alex-a11ahar/SolarEye-Security-System/Status Update 3 template.pptx.pdf

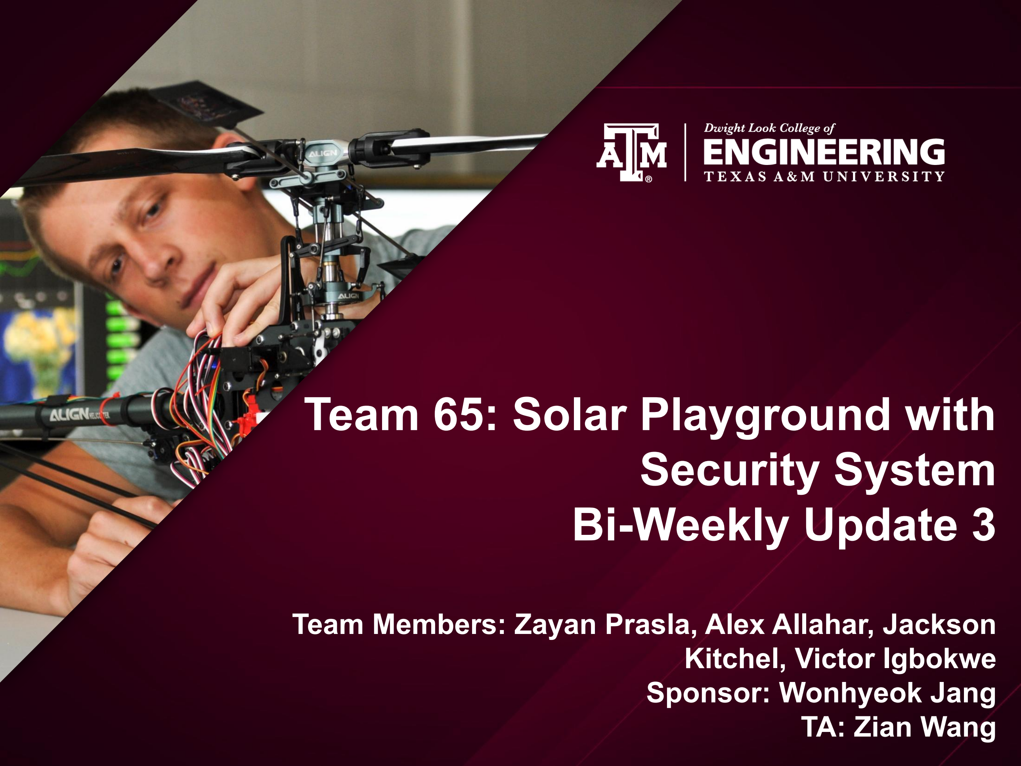
[picture p125: page 1]

# Team 65: Solar Playground with Security System Bi-Weekly Update 3

Team Members: Zayan Prasla, Alex Allahar, Jackson Kitchel, Victor Igbokwe
Sponsor: Wonhyeok Jang
TA: Zian Wang

# Project Summary

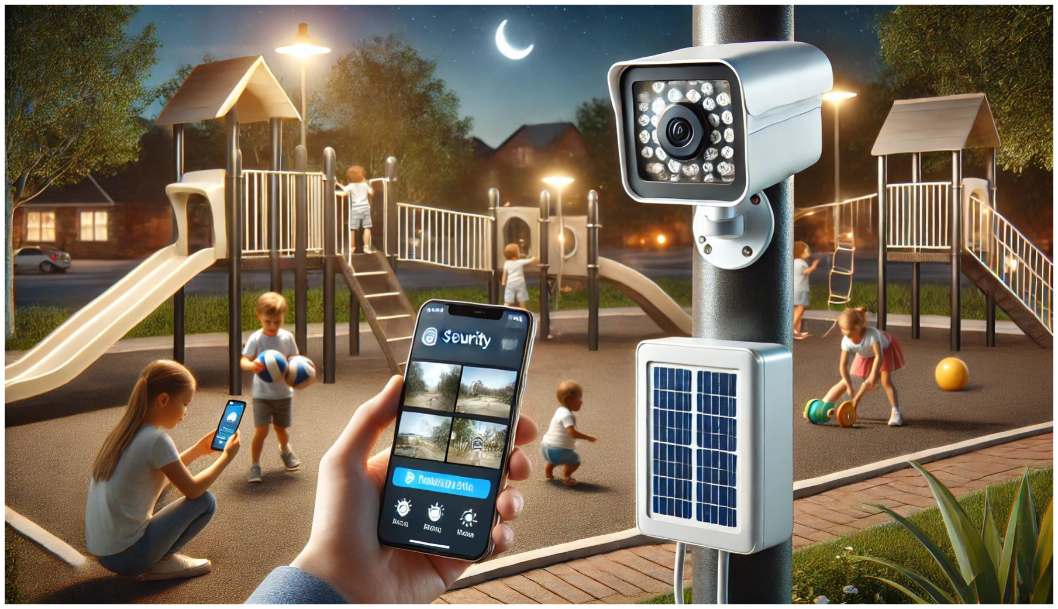
[picture p126: figure]

The SolarEye Security System is a solar-powered, autonomous
surveillance solution for playgrounds and parks.

It enhances security with
motion-activated cameras, real-time mobile alerts, LED deterrent lighting, and visitor charging stations.

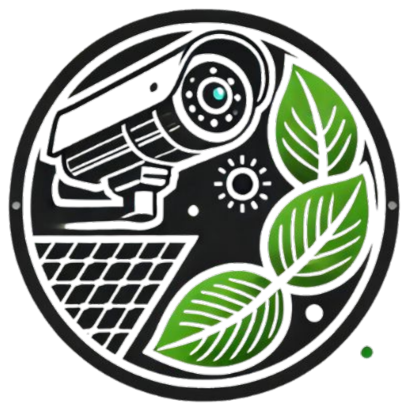
[picture p127: figure]

This eco-friendly system ensures continuous, cost-effective protection for private parks and properties.

# Project/Subsystem Overview

Red - Jackson Kitchel (Power Generation) Yellow - Victor Igbokwe (Power Distribution) Green - Alex Allahar (Microprocessor & Sensors) Blue - Zayan Prasla (Network & Application)

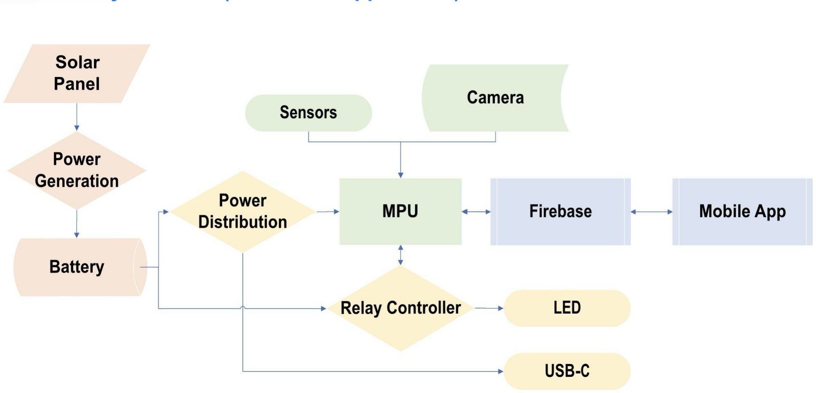
[picture p128: figure]

# Project Timeline

New PCBs
Ordered/
Received
(completed
02/03)

Integration
of MPU and
Application
subsystems
(to
completed
02/25)

Integration
of Power
Delivery
system with
MPU (to
complete by
02/25)

Integration of
Power
Generation
System with
Power
Delivery
System
(to complete
by 02/28)

Final
Integration
(to complete
by 03/03)

System Test
(to complete
by 03/10)

Validation
(to
complete by
03/20)

Demo and
Report
(to
complete
by 04/25)

# Power Generation

Accomplishments since last update 12 hrs of effort

Ongoing progress/problems and plans until the next presentation
- Both boards soldered
experienced issue of a
capacitor burning up
- Issue was found to be
component rated for wrong
amperage
- New component arrives
tomorrow
- Integrate with power distribution subsystem
- Test Current and Voltage sensor outputs with MCU
subsystem

# Power Generation

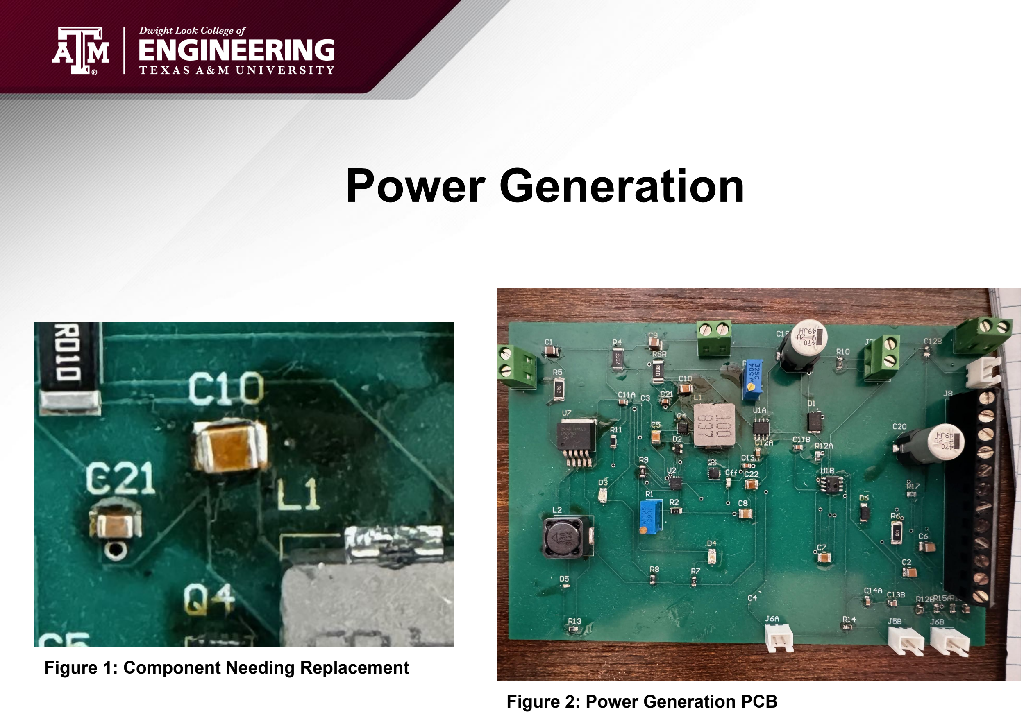
[picture p129: page 6]

Figure 1: Component Needing Replacement

Figure 2: Power Generation PCB

# Power Distribution

Accomplishments since last update 16 hrs of effort | Ongoing progress/problems and plans until the next presentation
❖ Successful Integration with Raspberry Pi MPU ❖ Soldered Relay Control module PCB | ❖ Validate Buck converter Integration for all modes of operation on MPU. ❖ Integration of relay control module PCB with Microprocessor system. ❖ Integration with

# Power Distribution

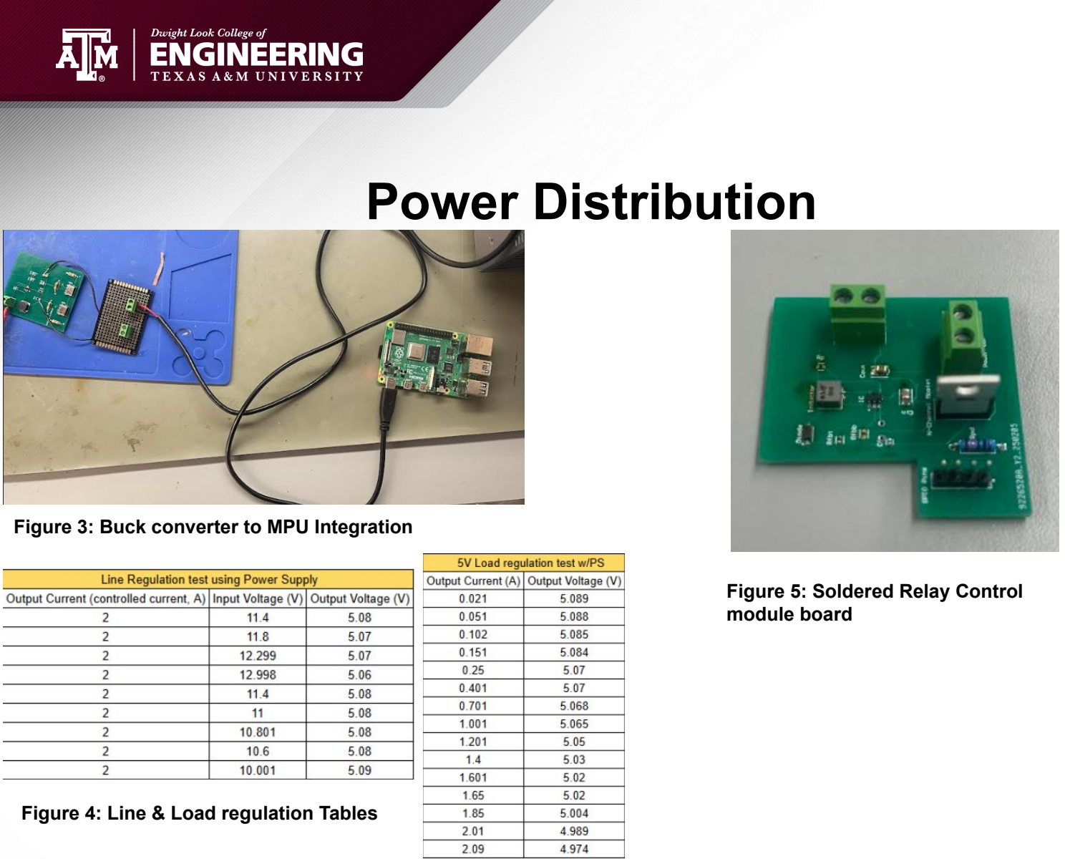
[picture p130: page 8]

Figure 3: Buck converter to MPU Integration

Figure 5: Soldered Relay Control module board

Figure 4: Line & Load regulation Tables

# Microprocessor & Sensors

Alex Allahar

Accomplishments since last update 17 hrs of effort

Ongoing progress/problems and plans until the next presentation ❖ Completed Integration of MPU with SolarEye App
❖ Integrated MPU with Buck Converter PCB
❖ Validated event detection to app delay

❖ Validate All Modes of Operation on Buck Converter PCB
❖ Validate Video Footage on Mobile App
❖ Complete Integration of Relay Controller PCB with MPU.
❖ Functionality Testing of App controlling Camera, LED, and sensor

# Microprocessor & Sensors

Alex Allahar

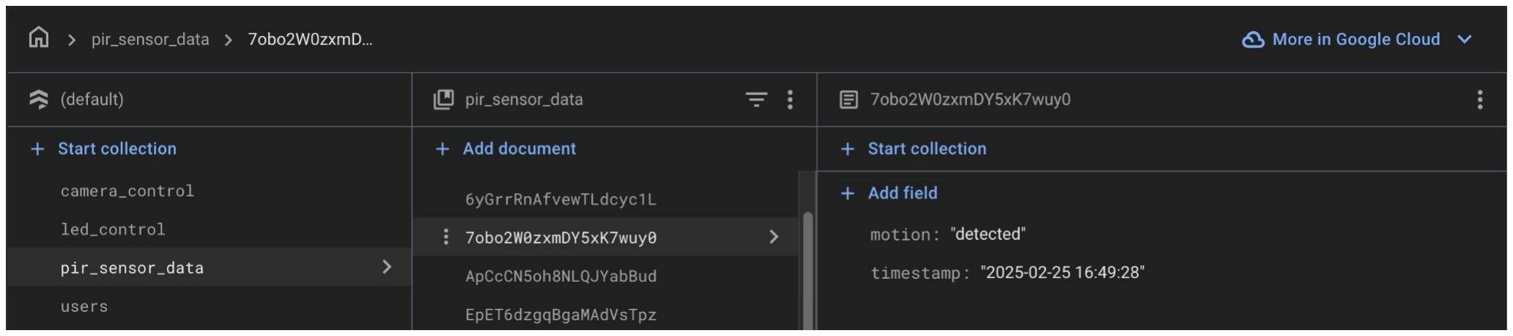
[picture p131: figure]

Figure 8: Event Detection Testcase Terminal

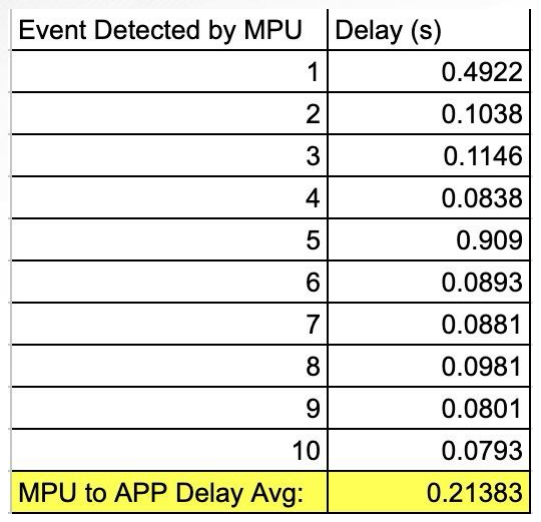
[picture p132: figure]

Figure 7: Firestore App Event History Database

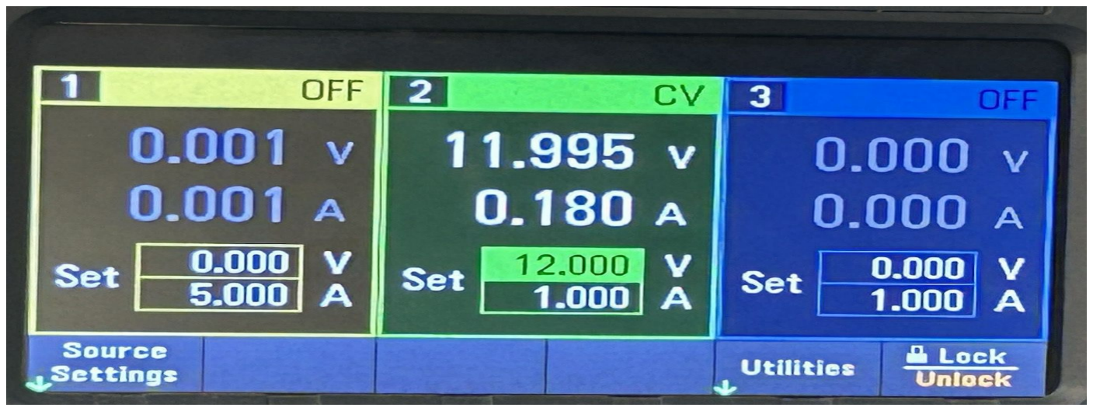
[picture p133: figure]

Figure 9: MPU Peak Current on Buck Converter PCB

Figure 6: MPU to App Delay Table

# Application & Network

Accomplishments since last update 12 hrs of effort

Ongoing progress/problems and plans until the next presentation ❖ Completed Integration between App and MPU
❖ Complete Camera/LED controls from app to Firebase to MPU ❖ Completed testing all backend security
❖ Instant updates to Event History

❖ Video and picture transfer from MPU to App
❖ Power level data
communication (Battery Level Graph)
❖ Lower power mode
❖ Live Streaming
❖ Ongoing updates to the
Frontend

# Application & Network

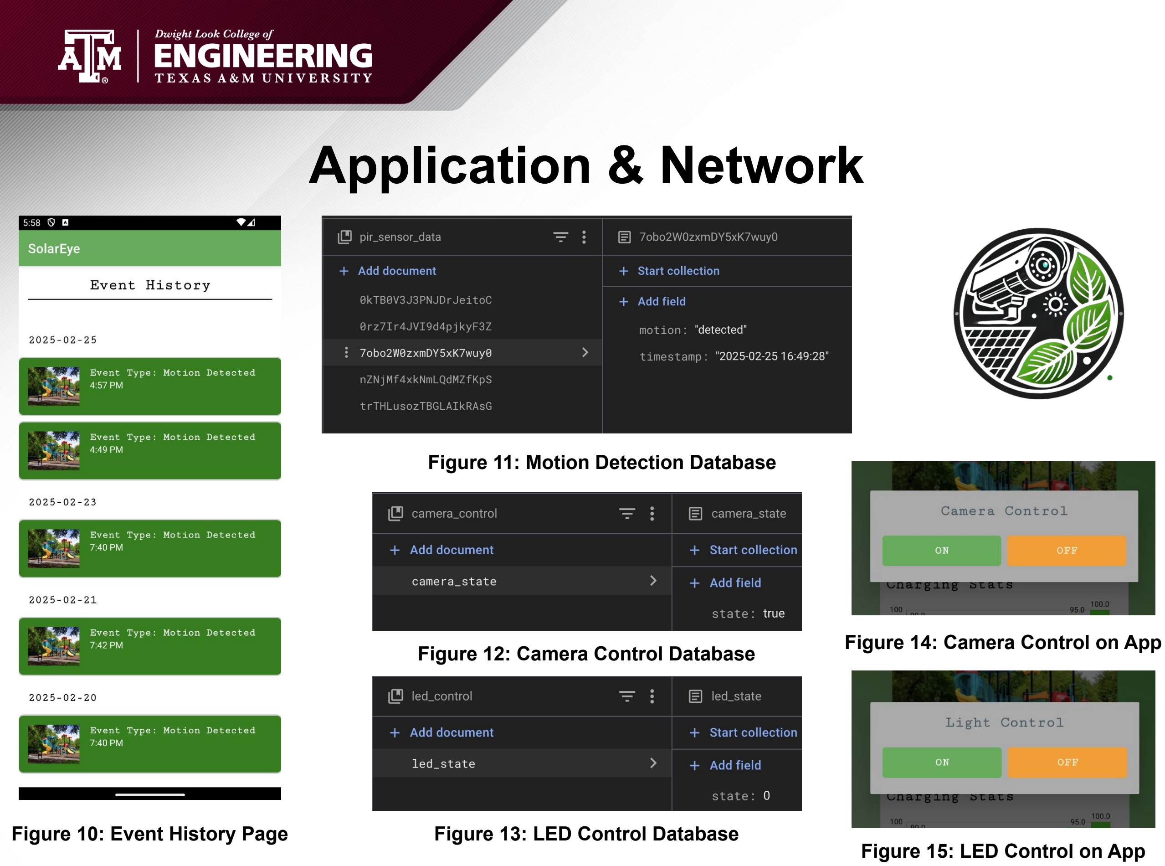
[picture p134: page 12]

Figure 10: Event History Page

Figure 11: Motion Detection Database

Figure 12: Camera Control Database

Figure 13: LED Control Database

Figure 14: Camera Control on App

Figure 15: LED Control on App

## Execution & Validation Plan

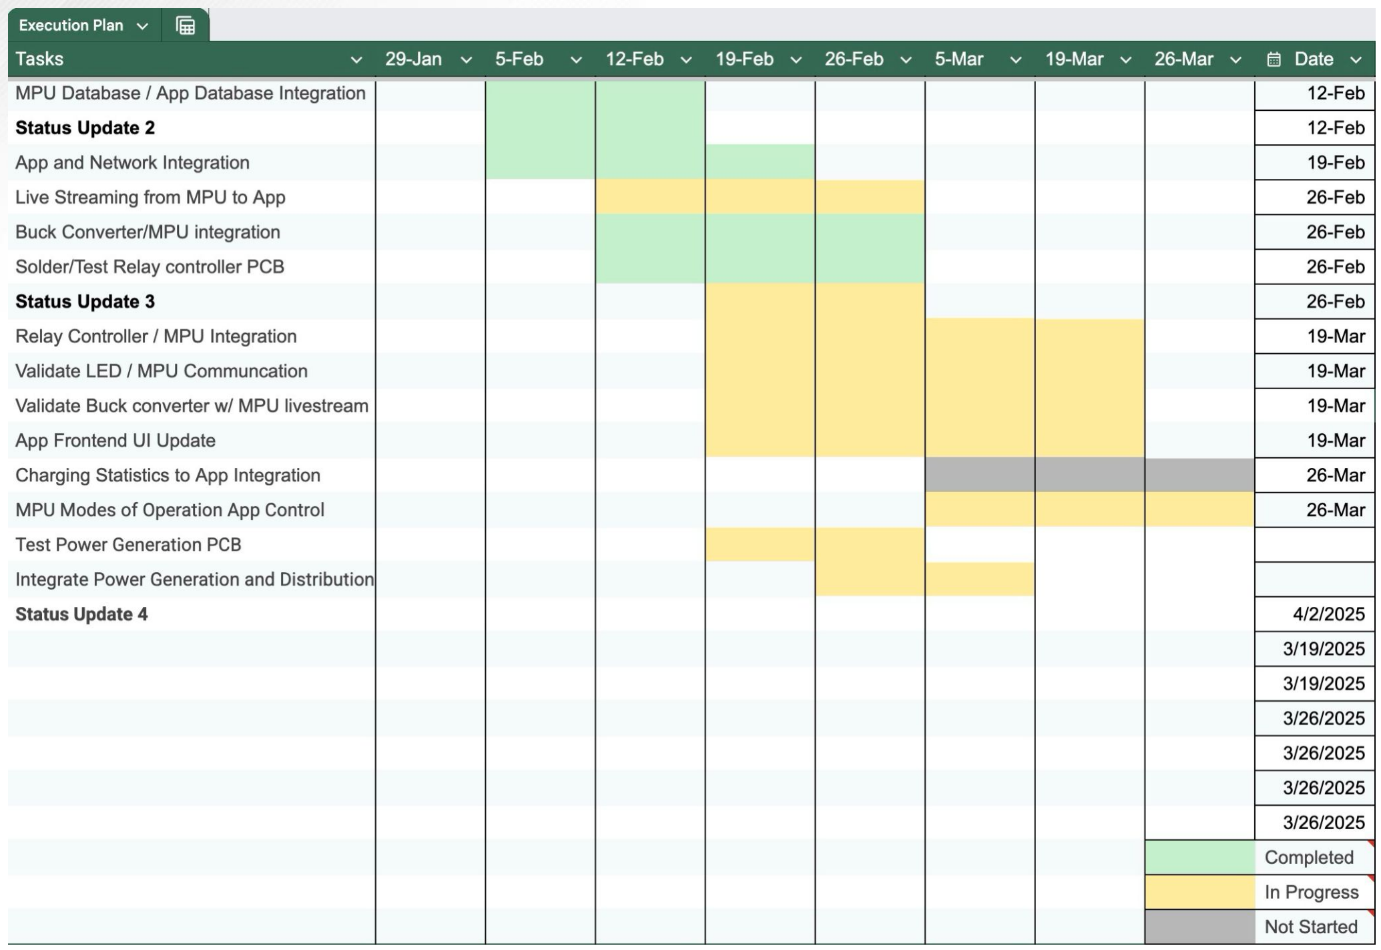
[picture p135: figure]

## Execution & Validation Plan

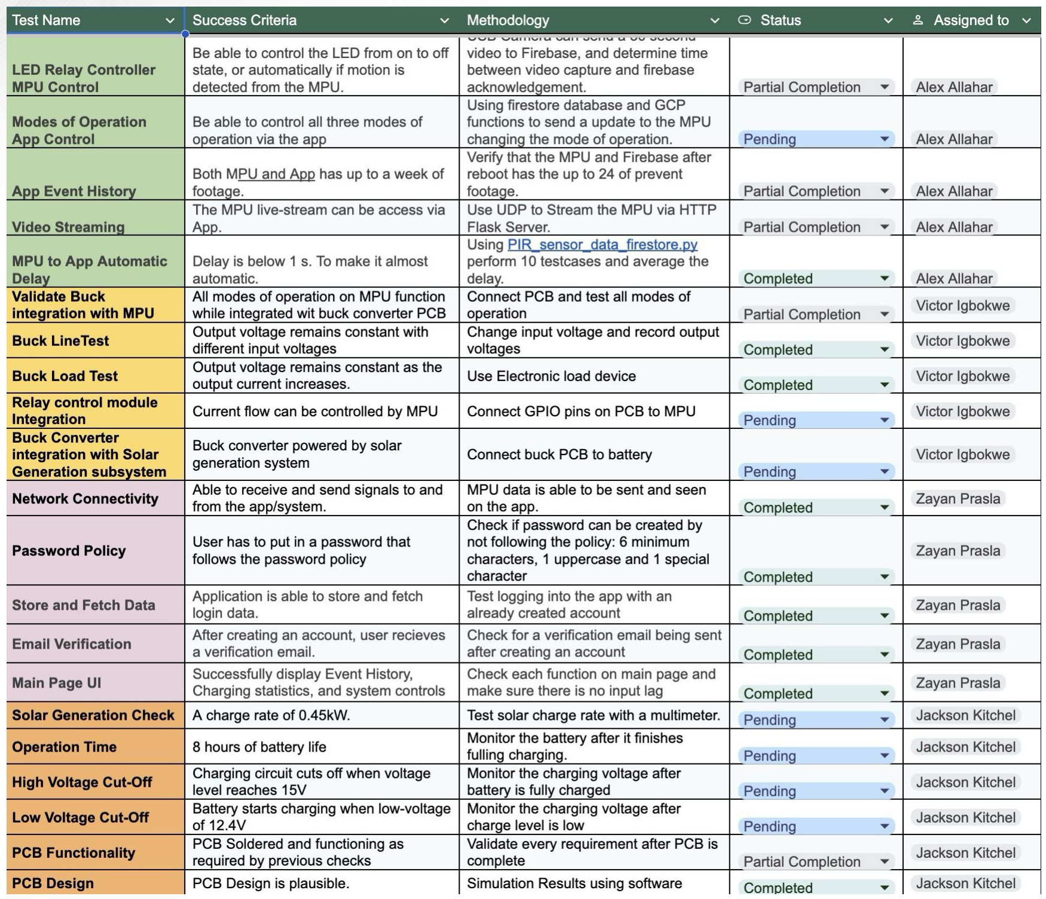
[picture p136: figure]

# Thank You
