alex-a11ahar/SolarEye-Security-System/Status Update 4 template.pptx.pdf

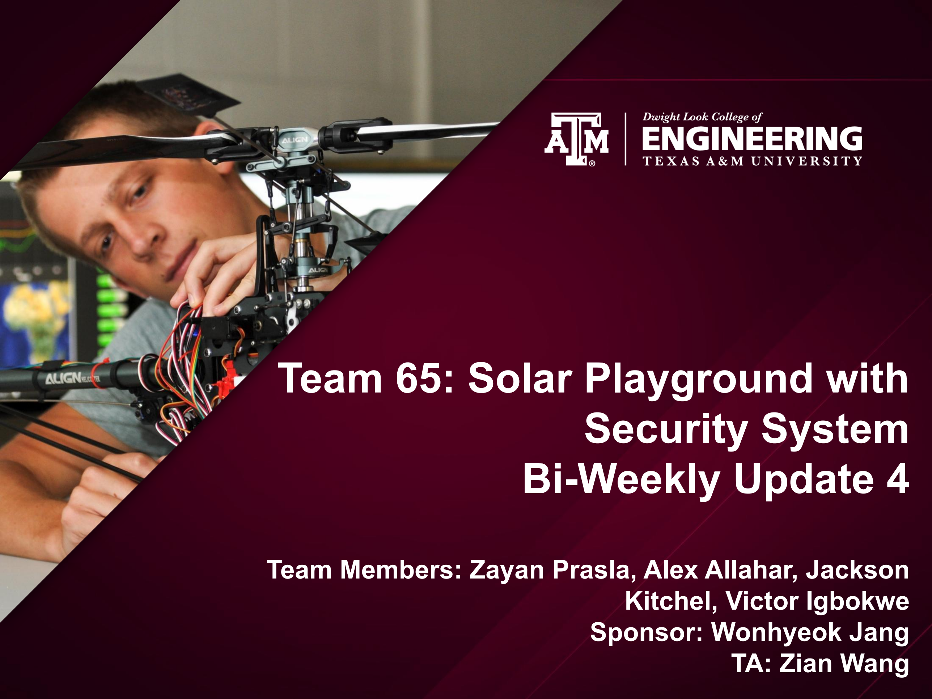
[picture p137: page 1]

# Team 65: Solar Playground with Security System Bi-Weekly Update 4

Team Members: Zayan Prasla, Alex Allahar, Jackson Kitchel, Victor Igbokwe
Sponsor: Wonhyeok Jang
TA: Zian Wang

# Project Summary


The SolarEye Security System is a solar-powered, autonomous
surveillance solution for playgrounds and parks.

It enhances security with
motion-activated cameras, real-time mobile alerts, LED deterrent lighting, and visitor charging stations.


This eco-friendly system ensures continuous, cost-effective protection for private parks and properties.

## Integrated System Diagram (Hardware)

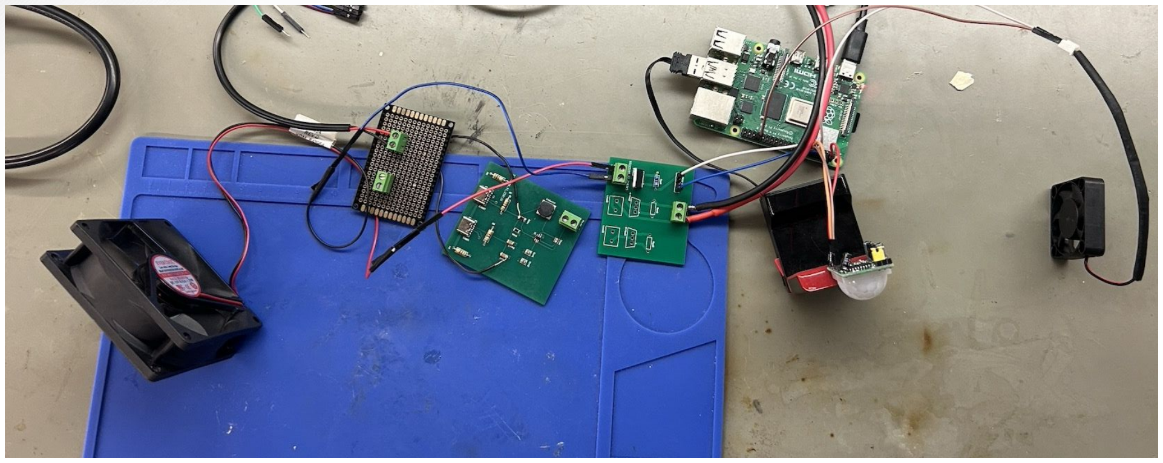
[picture p138: figure]

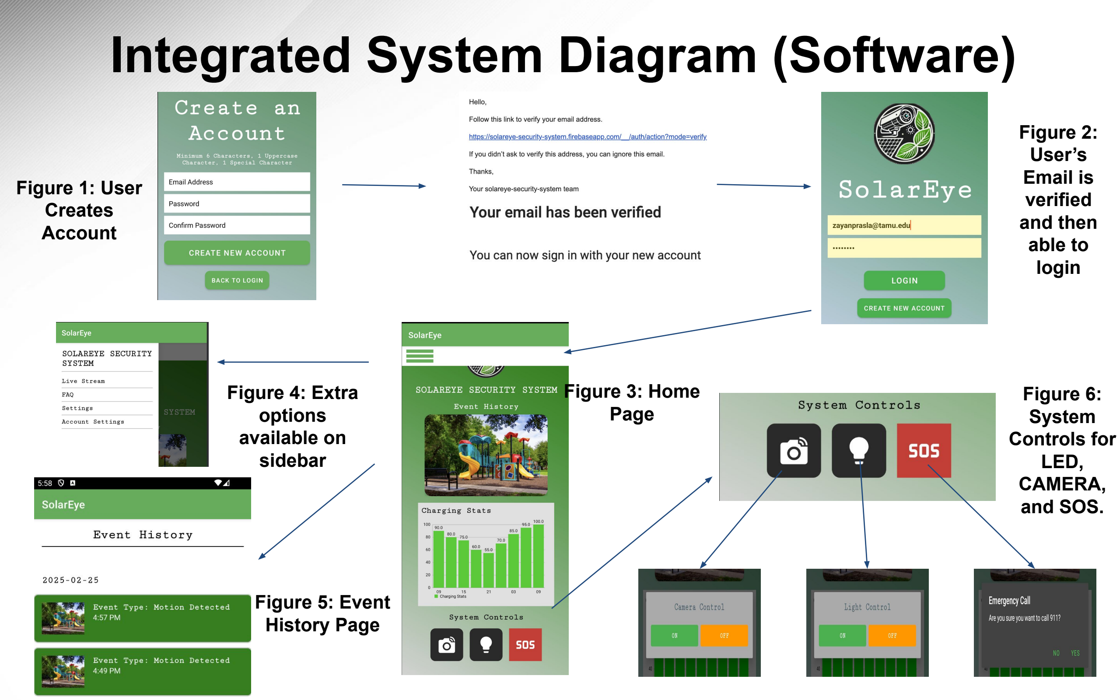
[picture p139: figure]
Integrated System Diagram (Software); Figure 1: User Creates Account; Figure 2: User’s Email is verified and then able to login; Figure 3: Home Page; Figure 6: System Controls for LED, CAMERA, and SOS.; Figure 5: Event History Page; Figure 4: Extra options available on sidebar

# Project Timeline

New PCBs
Ordered/
Received
(completed
02/03)

Integration
of MPU and
Application
subsystems
(to
completed
02/25)

Integration
of Power
Delivery
system with
MPU (to
complete by
02/25)

Integration of
Power
Generation
System with
Power
Delivery
System
(to complete
by 03/26)

System
Housing
(to complete
by 03/28)

Final
Integration
(to complete
by 04/10)

Validation
(to
complete by
04/20)

Demo and
Report
(to
complete
by 04/25)

# Jackson Kitchel

Accomplishments since last update 30 hrs of effort | Ongoing progress/problems and plans until the next presentation
❖ PCB was redesigned to fix capacitor problem and consolidate ❖ New PCB was soldered and tested ❖ Integration with solar panel and battery complete and tested | ❖ Integrate sensor outputs with MCU subsystem ❖ Start Housing ❖ Finish testing integration with power delivery subsystem

# Jackson Kitchel

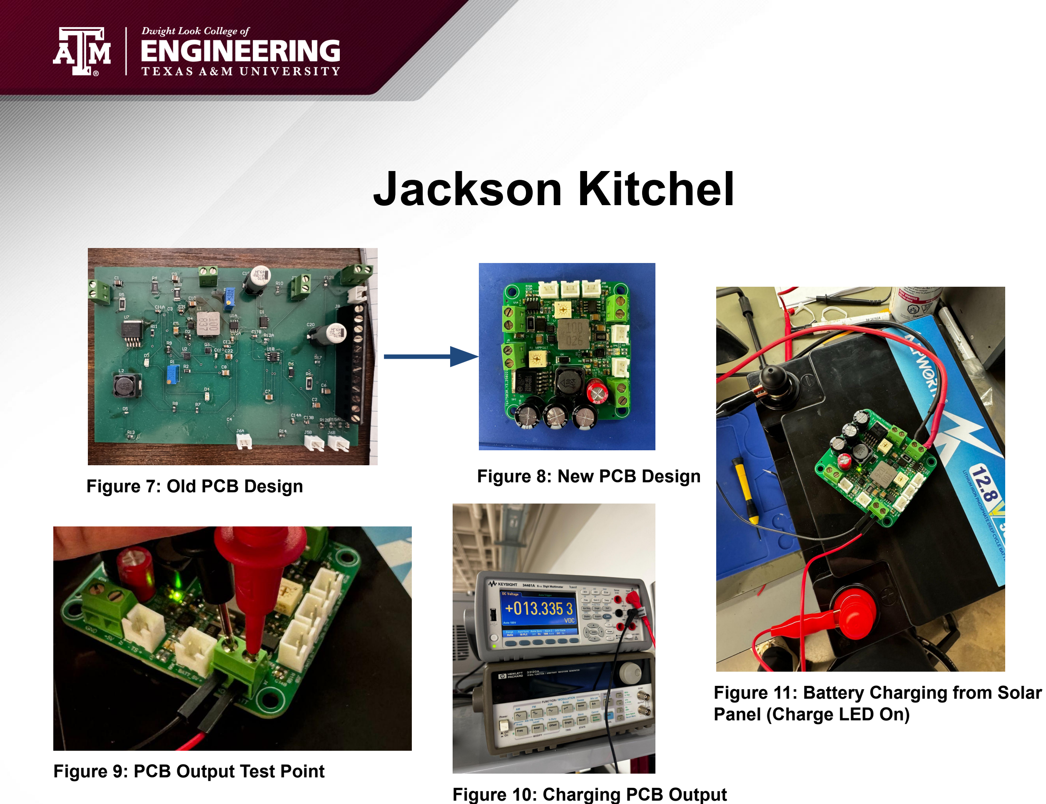
[picture p140: page 7]

Figure 7: Old PCB Design | Figure 8: New PCB Design

Figure 11: Battery Charging from Solar Panel (Charge LED On)

Figure 10: Charging PCB Output

Figure 9: PCB Output Test Point

# Victor Igbokwe

Accomplishments since last update 12 hrs of effort | Ongoing progress/problems and plans until the next presentation
❖ Integration of Power Distribution and MPU system completed ❖ Validated power outputs for different modes of operation with MPU | ❖ Integration with Power Generation system. ❖ Design/Build Housing for Circuit boards(During capstone blitz).

# Victor Igbokwe

Mode of Operation | Power Consumption(A)
Idle | 1.88 A
Event Detection | 3.65 A
Live Streaming | 2.15A

Figure 12: MPU Operating Modes and Corresponding Power Consumption Table

Media 1: Video showing the Buck converter supplying
power to MPU while
livestreaming

# Alex Allahar

Accomplishments since last update 8 hrs of effort | Ongoing progress/problems and plans until the next presentation
❖ Integrated Relay Controller PCB with MPU. ❖ Validate Event History on App Database ❖ Verified MPU / APP controls LED and cooling fans. | ❖ Validate Event History on Mobile App ❖ Start housing during Blitz.

# Alex Allahar

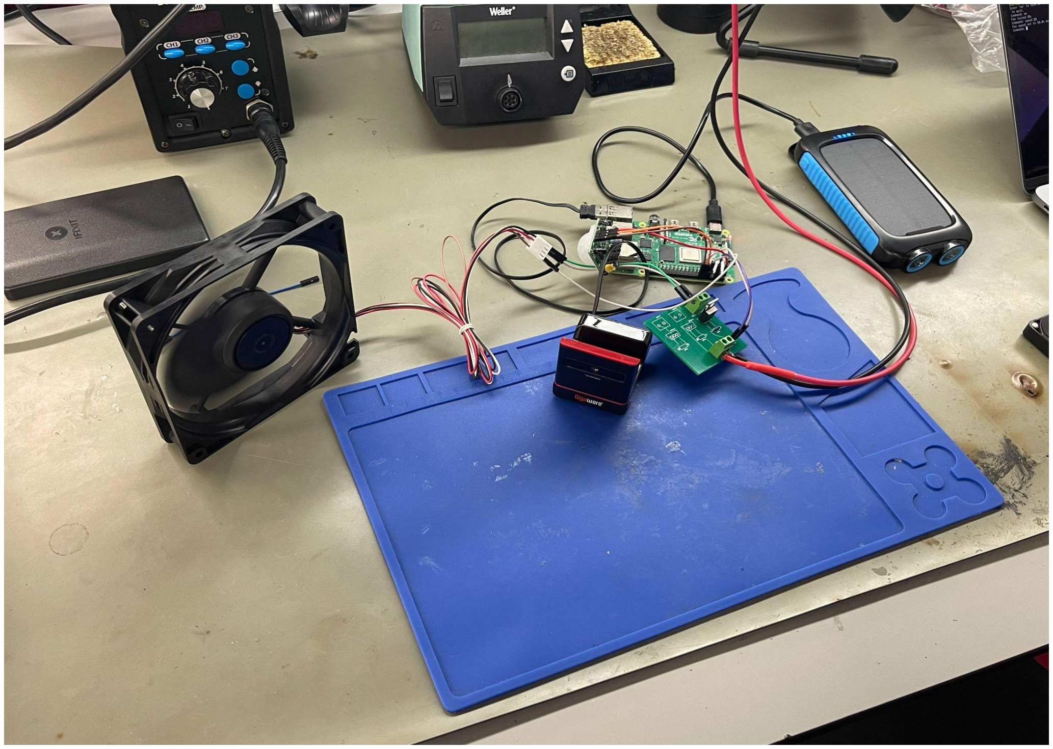
[picture p141: figure]

Figure 13: Fan Component Testing Setup and Table

Component | Power Consumption(A)
Small Fan (Fixed) | 0.6 A
Medium Fan (Fixed) | 1.16 A
Large Fan (Variable) | 7.017 A (100 %)

# Alex Allahar

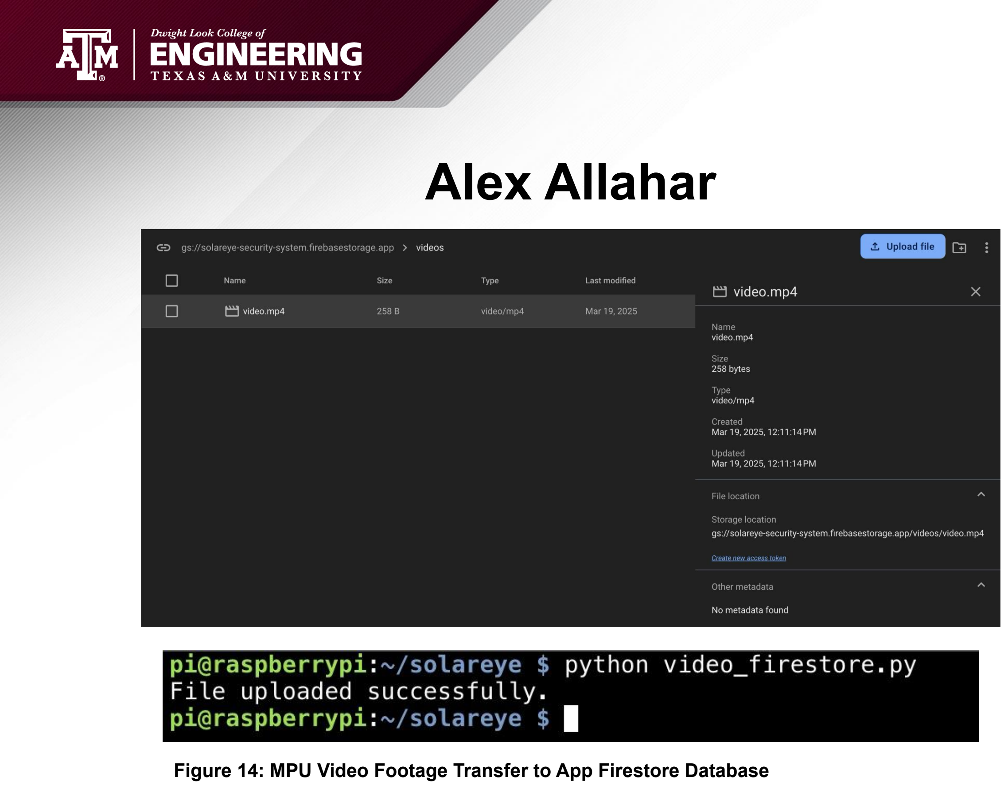
[picture p142: page 12]

Figure 14: MPU Video Footage Transfer to App Firestore Database

# Zayan Prasla

Accomplishments since last update 7 hrs of effort | Ongoing progress/problems and plans until the next presentation
❖ Validated all button communication from App to MCU ❖ Continuous tweaks to the frontend to for smoothest app experience | ❖ Validate thumbnail (picture)/video transfer from mcu to app ❖ Validate live streaming ❖ Power level communication ❖ Validate Low power mode

# Zayan Prasla

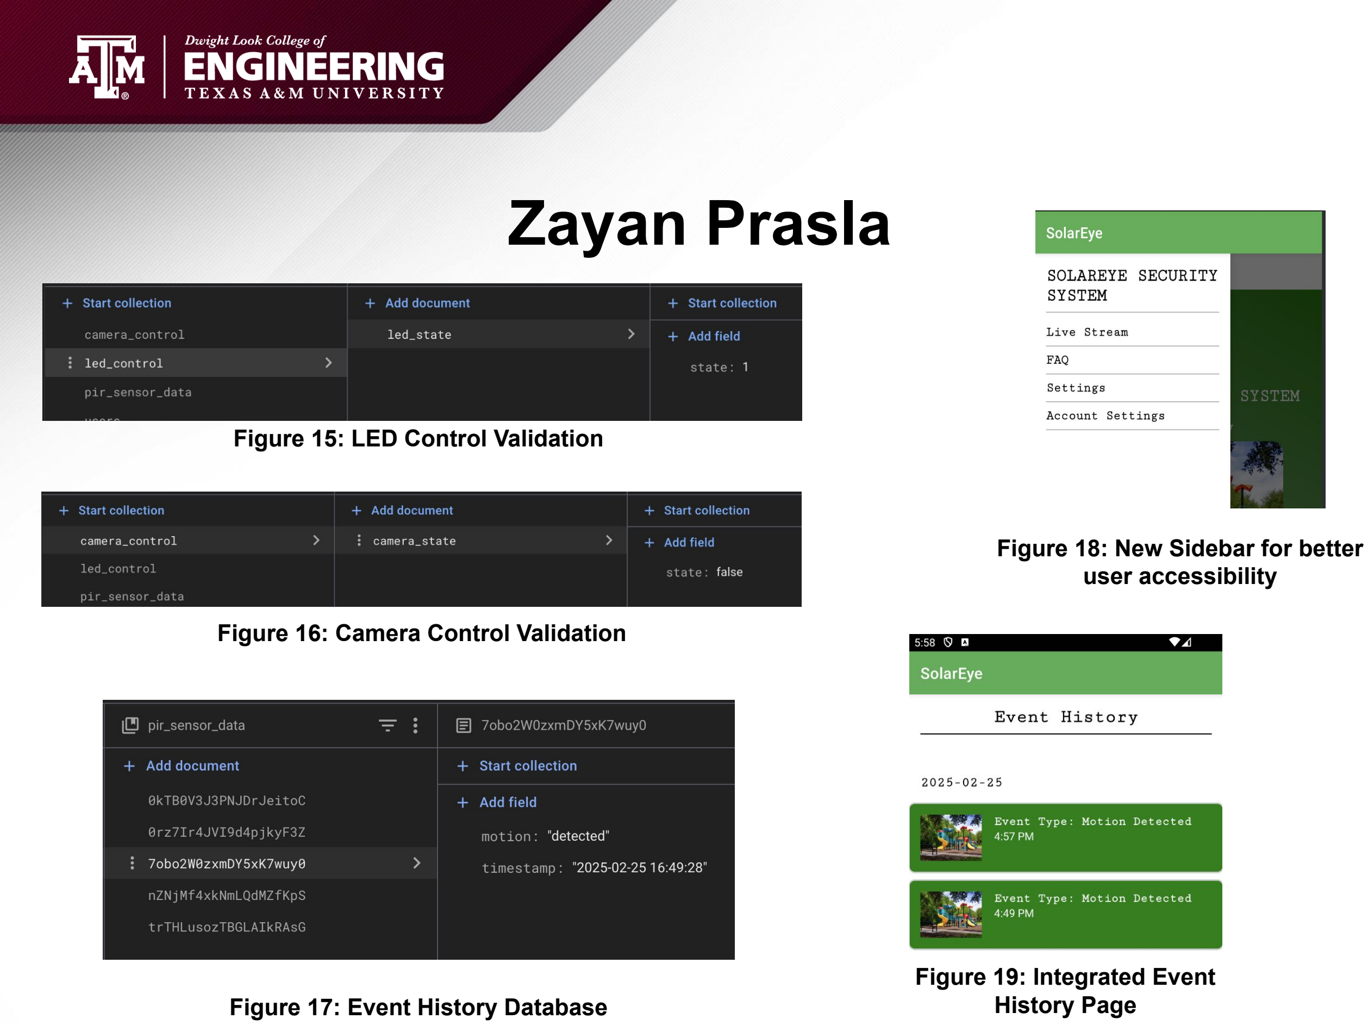
[picture p143: page 14]

Figure 18: New Sidebar for better user accessibility

Figure 15: LED Control Validation

Figure 16: Camera Control Validation

Figure 17: Event History Database

Figure 19: Integrated Event History Page

# Execution Plan

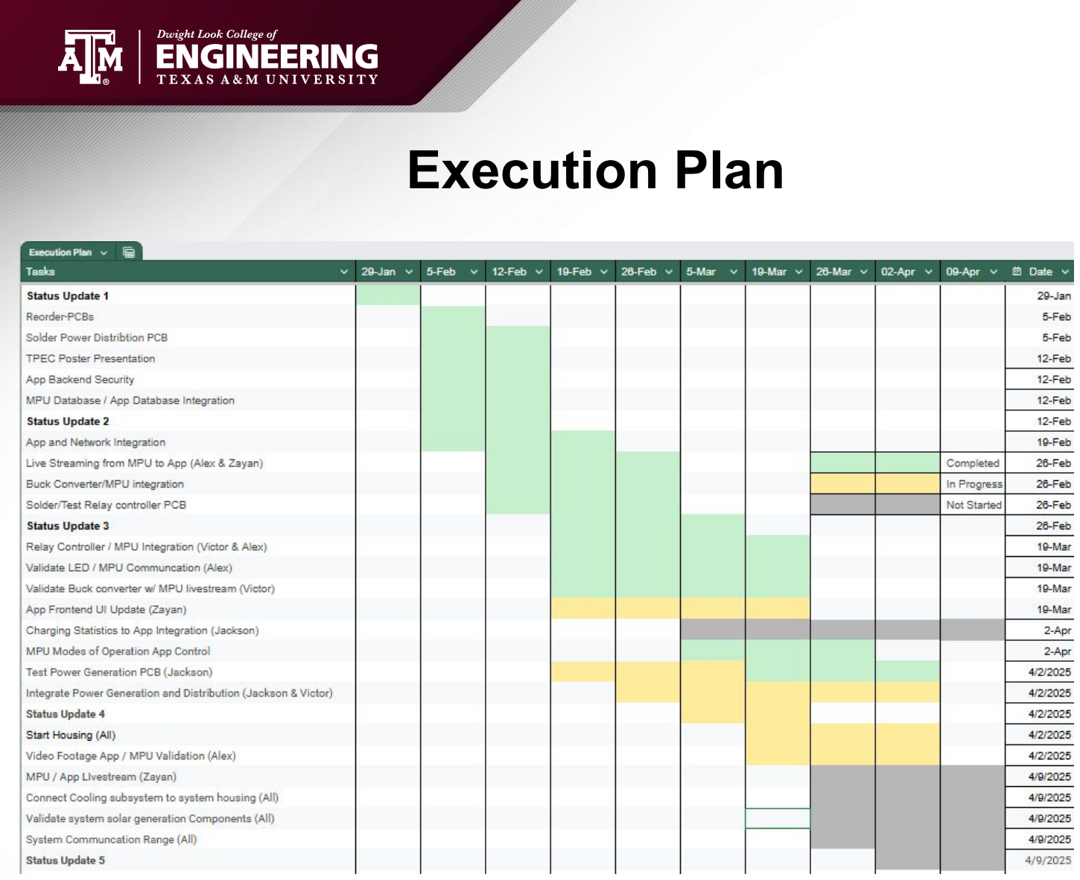
[picture p144: page 15]

# SYSTEM Validation Plan

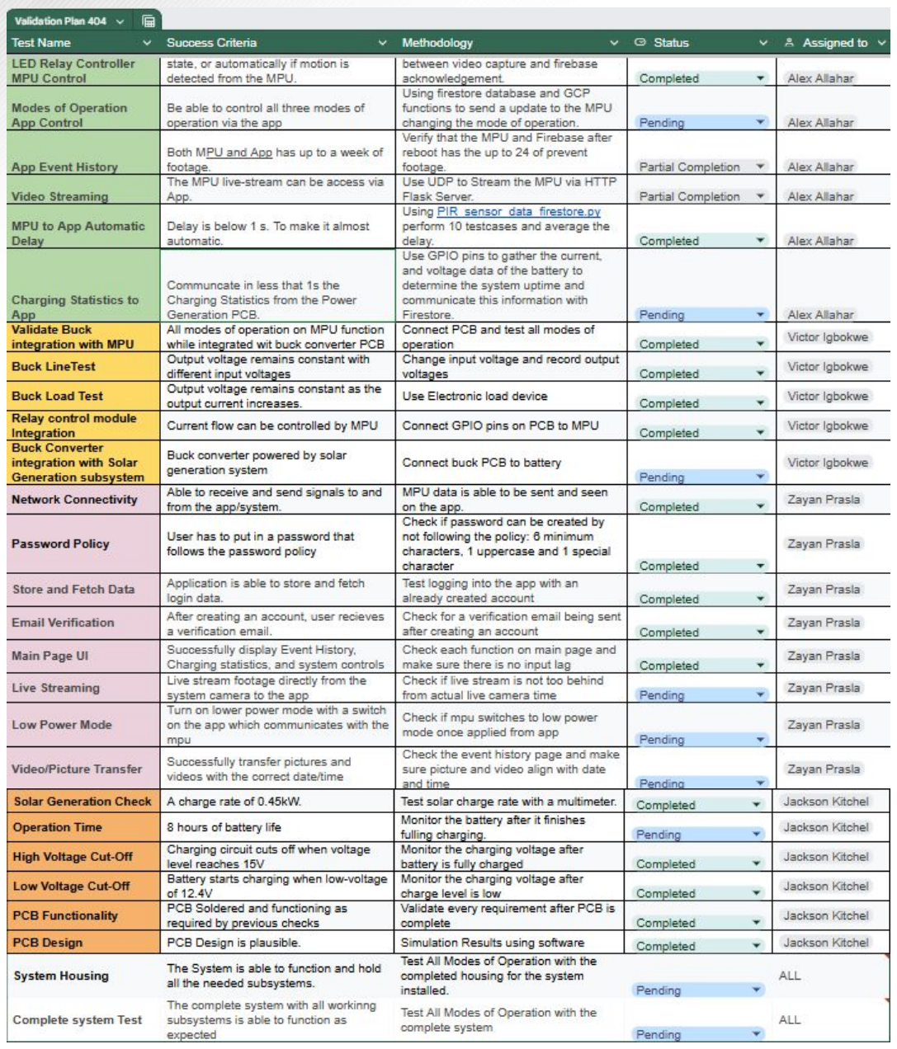
[picture p145: figure]

# Thank You!
