alex-a11ahar/SolarEye-Security-System/Status Update 5 template.pptx.pdf

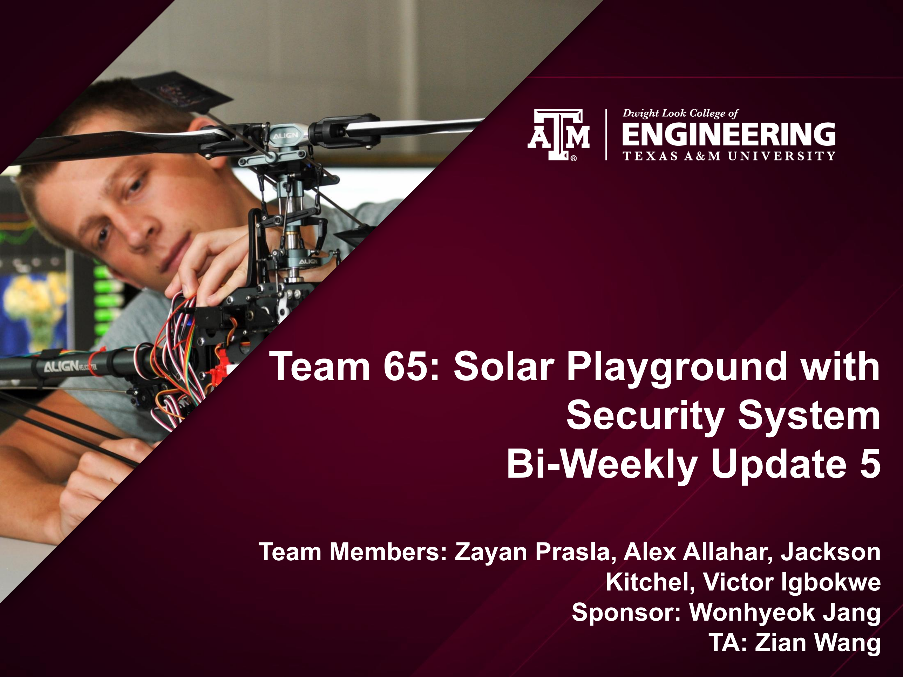
[picture p146: page 1]

# Team 65: Solar Playground with Security System Bi-Weekly Update 5

Team Members: Zayan Prasla, Alex Allahar, Jackson Kitchel, Victor Igbokwe
Sponsor: Wonhyeok Jang
TA: Zian Wang

# Project Summary


The SolarEye Security System is a solar-powered, autonomous
surveillance solution for playgrounds and parks.

It enhances security with
motion-activated cameras, real-time mobile alerts, LED deterrent lighting, and visitor charging stations.


This eco-friendly system ensures continuous, cost-effective protection for private parks and properties.

## Integrated System Diagram (Hardware)

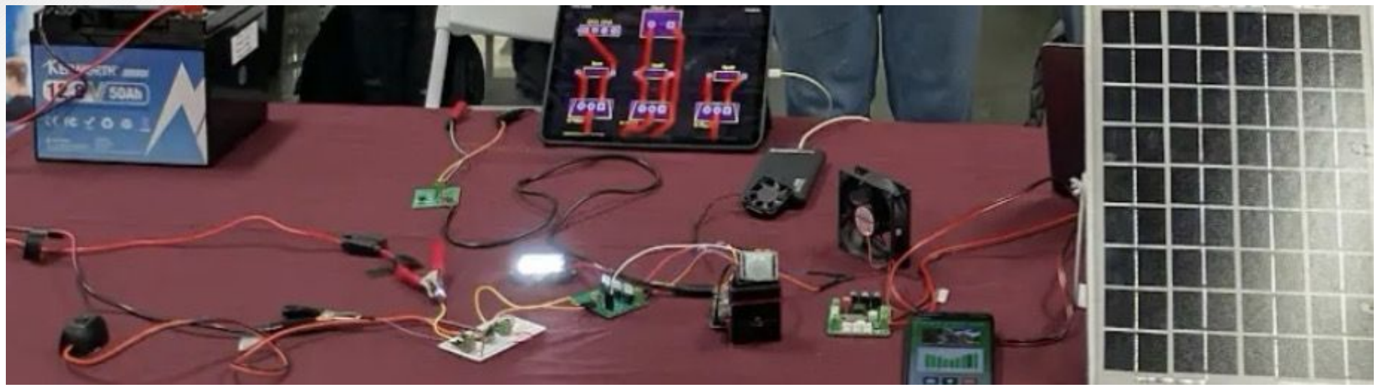
[picture p147: figure]

Figure 1: Full System Open Housing Diagram

# Integrated System Diagram (Software)

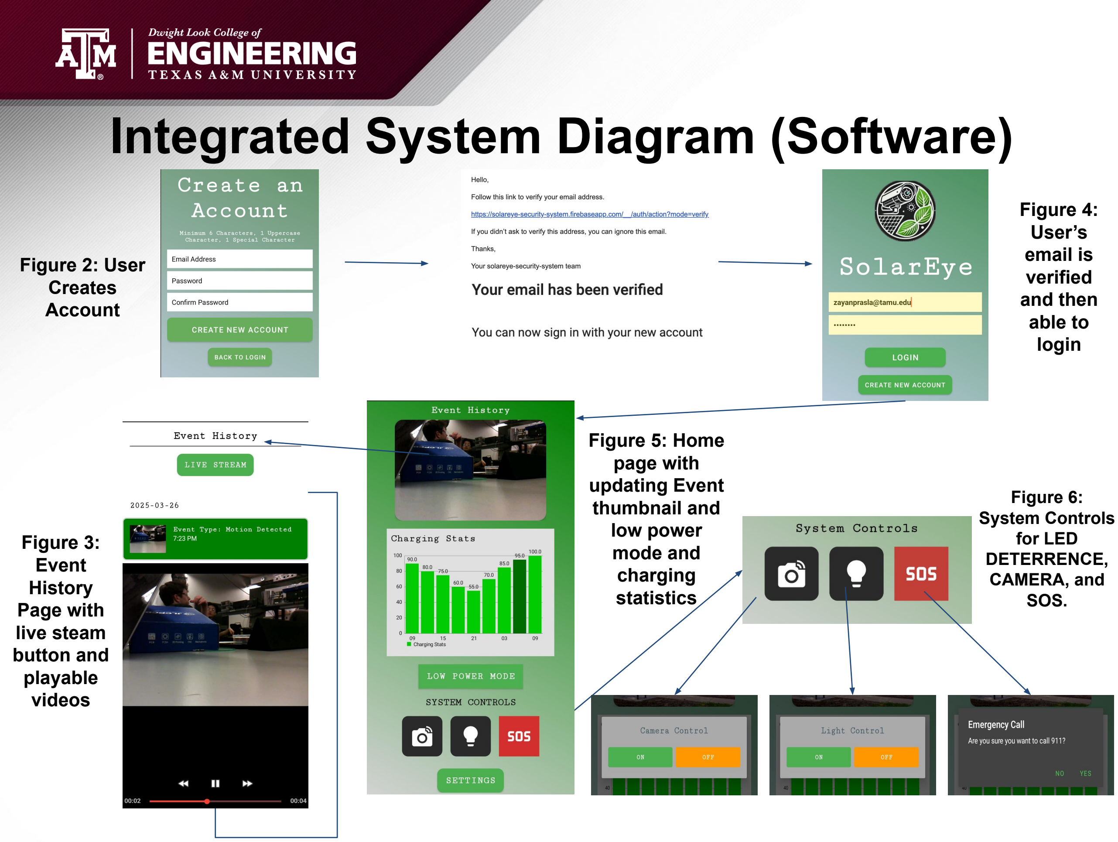
[picture p148: page 4]

Figure 2: User
Creates
Account

Figure 4:
User’s
email is
verified
and then
able to
login

Figure 5: Home
page with
updating Event
thumbnail and
low power
mode and
charging
statistics

Figure 6:
System Controls
for LED
DETERRENCE,
CAMERA, and
SOS.

Figure 3:
Event
History
Page with
live steam
button and
playable
videos

# Project Timeline

New PCBs
Ordered/
Received
(completed
02/03)

Integration
of MPU and
Application
subsystems
(to
completed
02/25)

Integration
of Power
Delivery
system with
MPU (to
complete by
02/25)

Integration of
Power
Generation
System with
Power
Delivery
System
(to complete
by 03/26)

Final
Integration
(to complete
by 04/10)

System
Housing
(to complete
by 04/10)

Validation
(to
complete by
04/20)

Demo and
Report
(to
complete
by 04/25)

# Jackson Kitchel

Accomplishments since last update 9 hrs of effort | Ongoing progress/problems and plans until the next presentation
❖ Sensors have been connected via ADC to MCU ❖ Finished integration with Power Distribution Subsystem | ❖ Finish setting up sensor algorithms in coordination with MCU subsystem ❖ Housing

# Jackson Kitchel

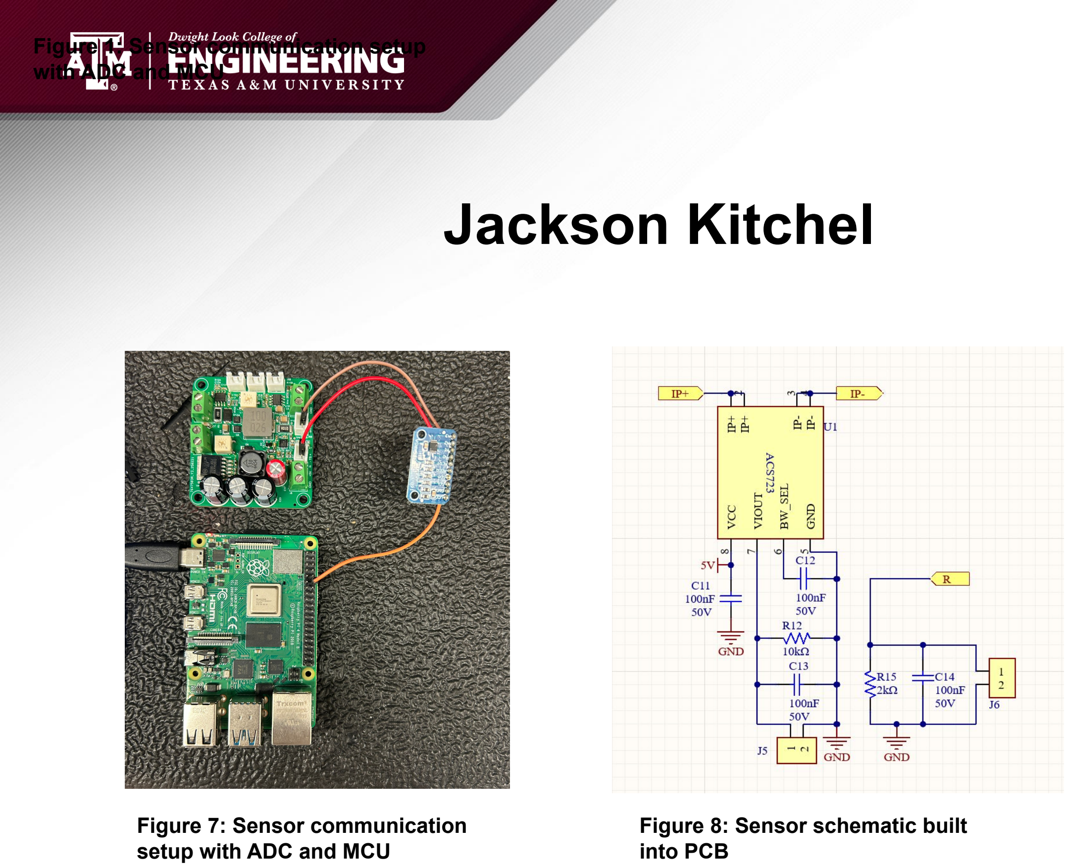
[picture p149: page 7]

Figure 7: Sensor communication setup with ADC and MCU

Figure 1: Sensor communication setup with ADC and MCU

Figure 8: Sensor schematic built into PCB

# Victor Igbokwe

Accomplishments since last update 13 hrs of effort | Ongoing progress/problems and plans until the next presentation
❖ Finished Integration with Power Generation Subsystem ❖ Created a Switchboard to improve safety when dealing with battery. | ❖ Finish Up Housing Box ❖ House PCBs and other devices in box

# Victor Igbokwe

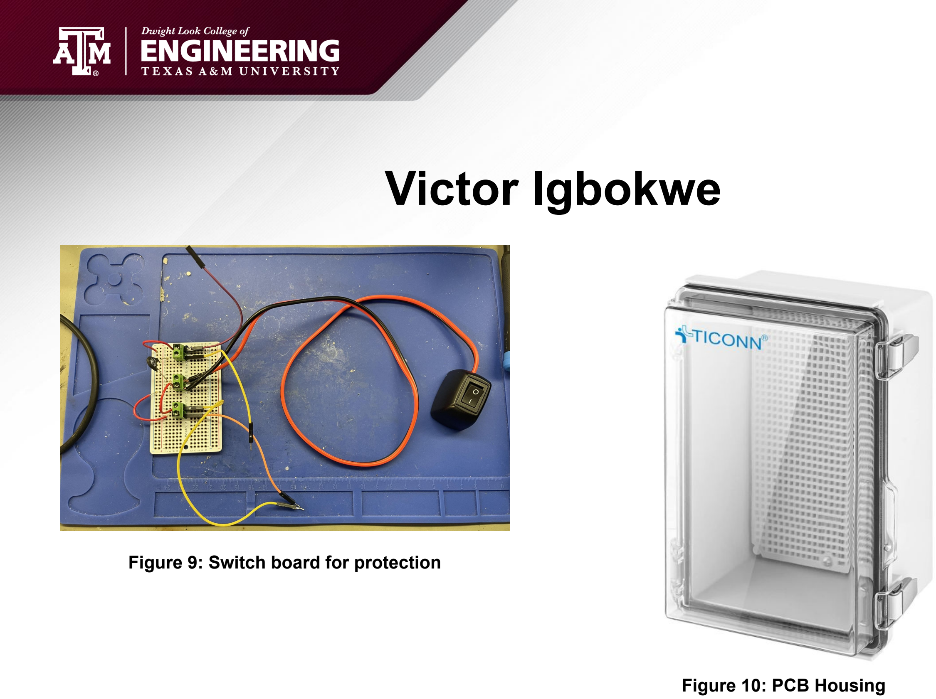
[picture p150: page 9]

Figure 9: Switch board for protection

Figure 10: PCB Housing

# Alex Allahar

Accomplishments since last update 12 hrs of effort | Ongoing progress/problems and plans until the next presentation
❖ Developed LED Deterrence Button for App ❖ Tested ADC I2C communication with Power Generation PCB | ❖ Replace Camera ❖ Validate Charging Statistics ❖ Complete Housing

# Alex Allahar

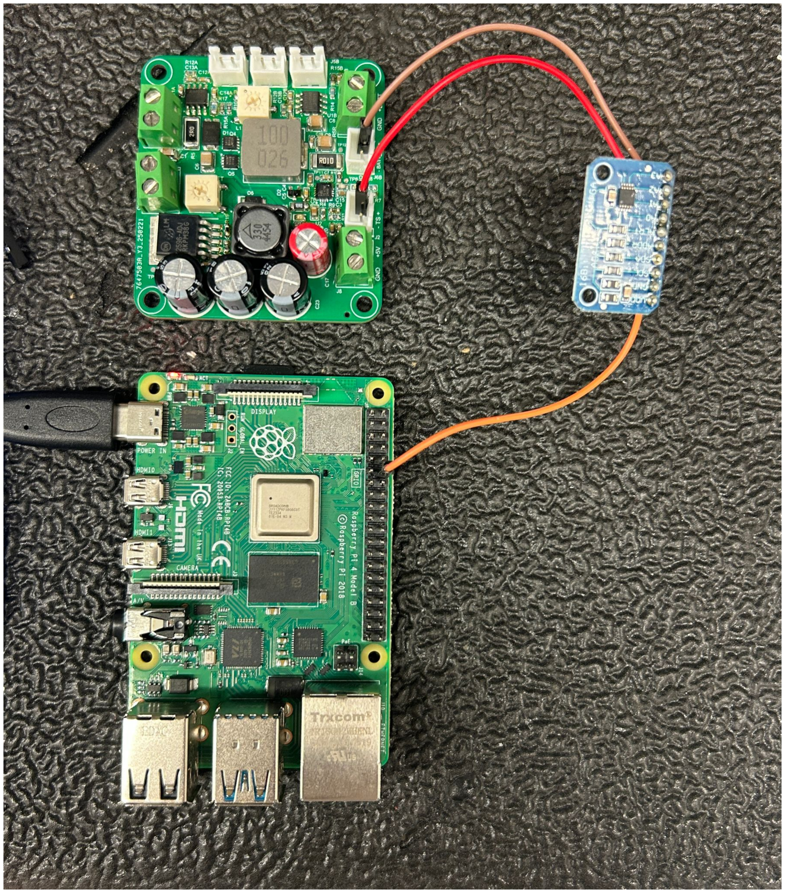
[picture p151: figure]
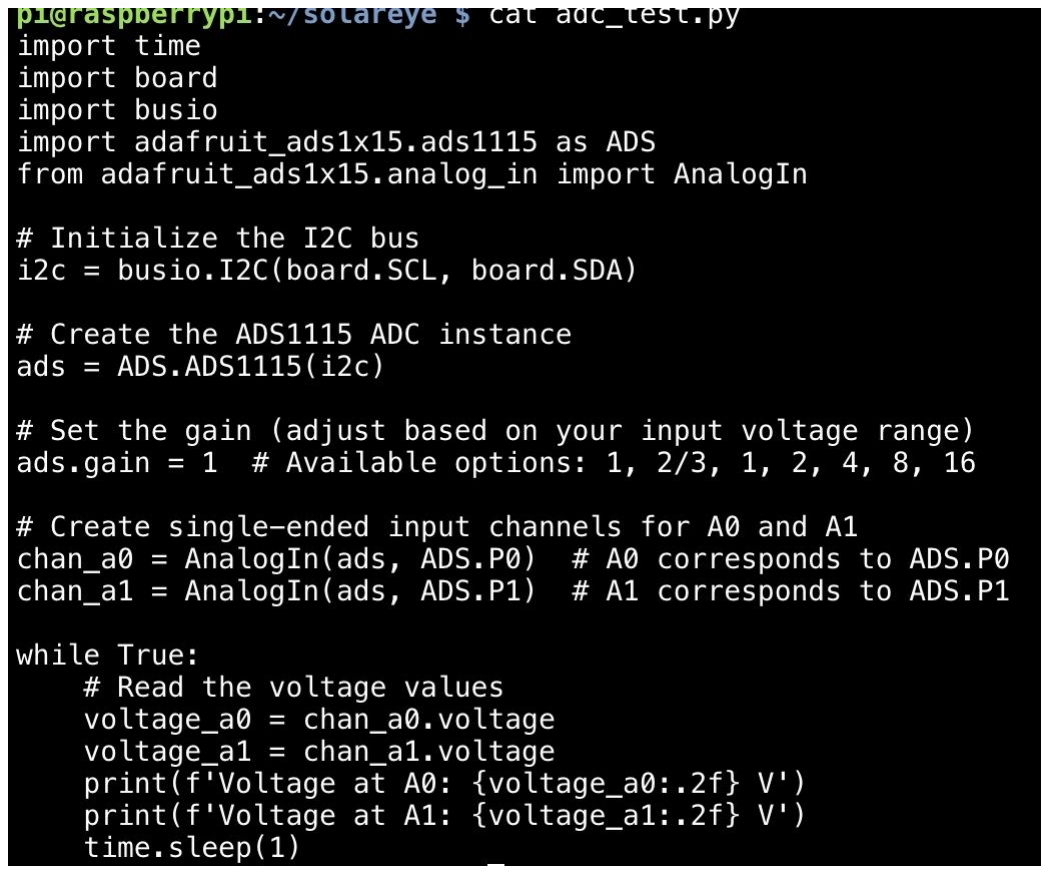
[picture p152: figure]

Figure 11: ADS 1115 Code / Setup

# Zayan Prasla

Accomplishments since last update 11 hrs of effort

Ongoing progress/problems and plans until the next presentation ❖ Successfully validated video data transfer from MCU to app ❖ Updated event history
thumbnail on home page to
dynamically display the latest detection
❖ Implemented buttons for live streaming and low power mode functionalities

❖ Validate/test Low Power mode ❖ Validate/test Live Streaming ❖ Validate/test charging statistics

# Zayan Prasla

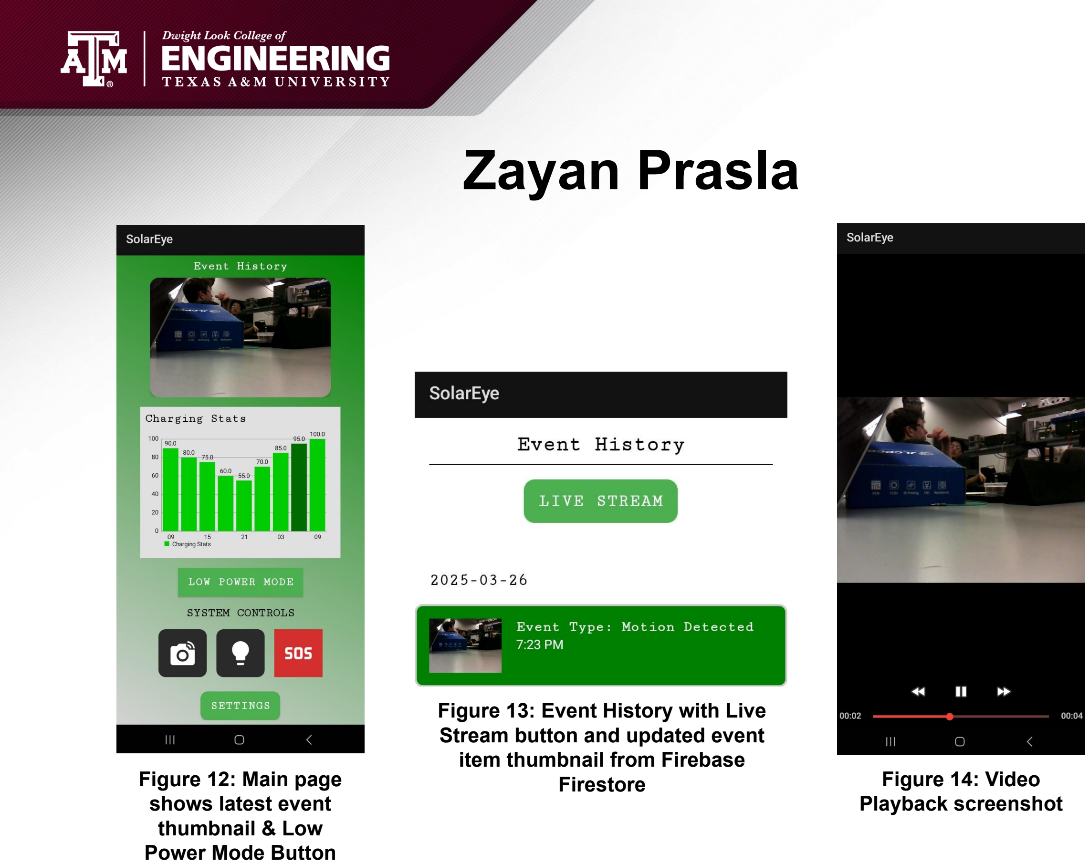
[picture p153: page 13]

Figure 12: Main page
shows latest event
thumbnail & Low
Power Mode Button

Figure 14: Video
Playback screenshot

Figure 13: Event History with Live Stream button and updated event item thumbnail from Firebase Firestore

# Execution Plan

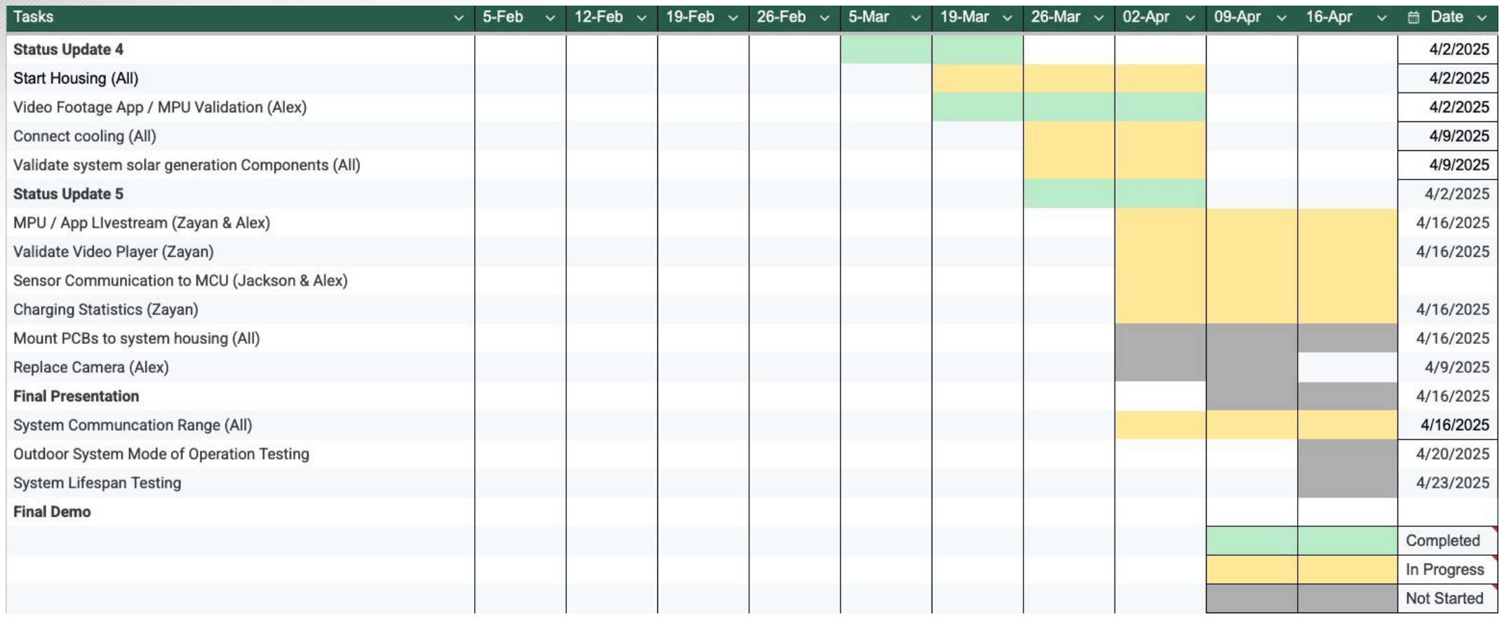
[picture p154: figure]

# SYSTEM Validation Plan Part 1

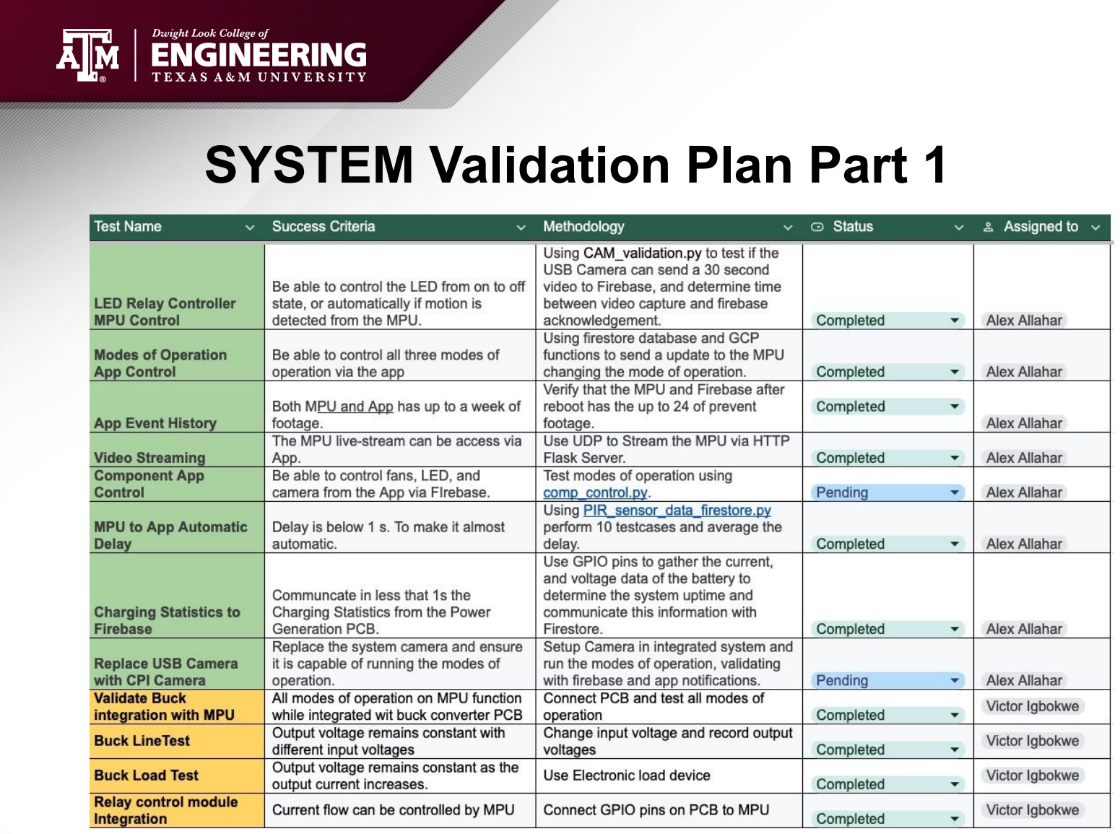
[picture p155: page 15]

# SYSTEM Validation Plan Part 2

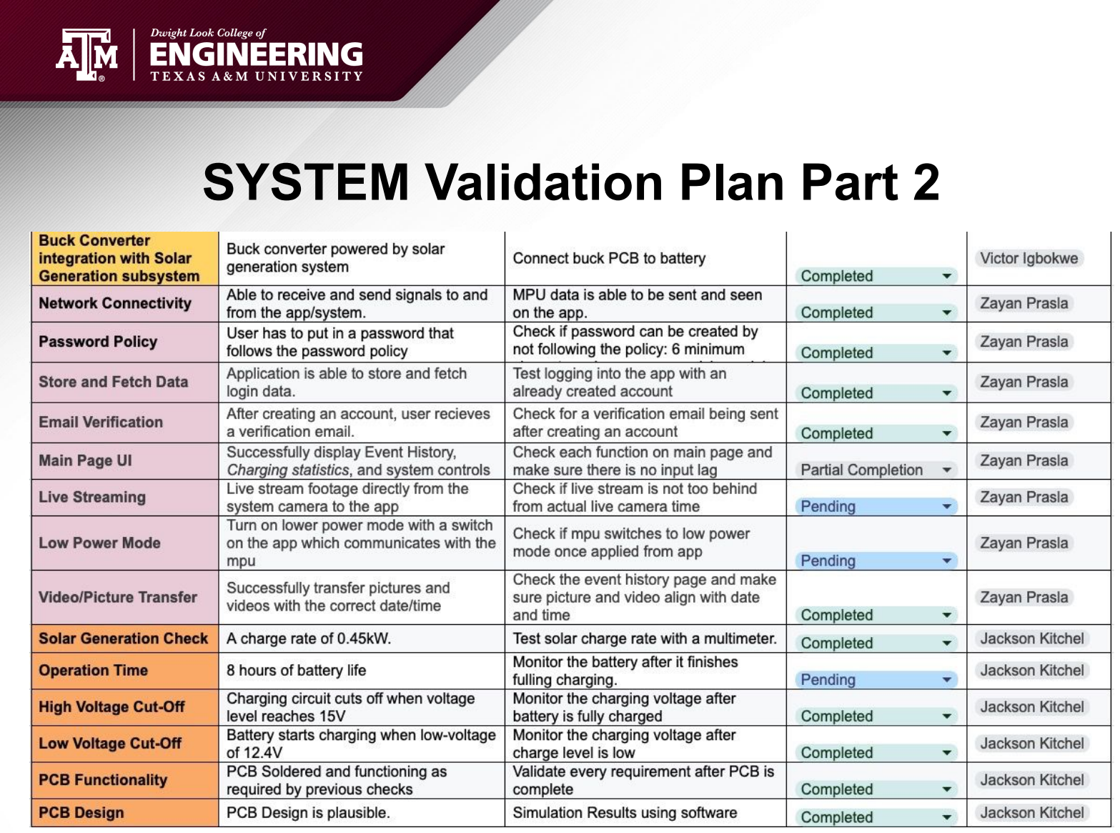
[picture p156: page 16]
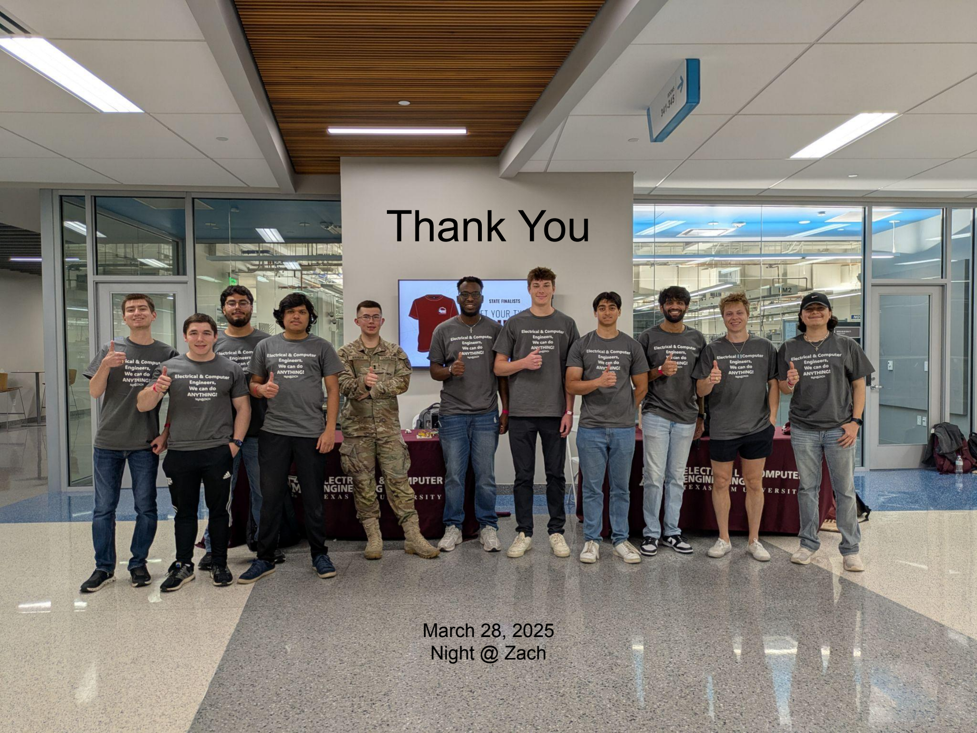
[picture p157: page 17]

# Thank You

# Thank You

March 28, 2025
Night @ Zach
